lxschwalb/tone_ale/tone_ale_common/tone_ale.h

/**
 * Copyright (c) 2023 Tone Age Technology
 *
 * SPDX-License-Identifier: BSD-3-Clause
 */
void tone_ale_pins_setup();
void tone_ale_capsense_setup();
void juggle_buffers();
void tone_ale_clk_setup(float sample_rate, float system_clk);
void tone_ale_i2cv_setup(int32_t *buff, int buffsize, void interrupt_service_routine());
int32_t * mutable_data();
uint32_t i2cv_missed_deadlines(); // blocks where the ISR ran over a block period late (audio likely glitched)
void set_led(bool state);
int32_t clip_shift(int32_t x);

class Capsense
{
    int max = 0;
    int min = __INT_MAX__;
    bool pressing = false;
    bool state = false;

public:
    void reset();
    bool capsense_button(float threshold);
    bool capsense_momentary_button(int threshold);
    float capsense_return_percentage_of_max();
};

#define SIN_BUFFSIZE    256

static float sin[SIN_BUFFSIZE] = {0.00000000e+00,  2.46374492e-02,  4.92599411e-02,  7.38525275e-02,
                                    9.84002783e-02,  1.22888291e-01,  1.47301698e-01,  1.71625679e-01,
                                    1.95845467e-01,  2.19946358e-01,  2.43913720e-01,  2.67733003e-01,
                                    2.91389747e-01,  3.14869589e-01,  3.38158275e-01,  3.61241666e-01,
                                    3.84105749e-01,  4.06736643e-01,  4.29120609e-01,  4.51244057e-01,
                                    4.73093557e-01,  4.94655843e-01,  5.15917826e-01,  5.36866598e-01,
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
                                -6.45928062e-01, -6.64540179e-01, -6.82748855e-01, -7.00543038e-01,
                                -7.17911923e-01, -7.34844967e-01, -7.51331890e-01, -7.67362681e-01,
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
