lxschwalb/tone_ale/tone_ale_common/filter_coefs.h

// Coeffs for a bpf filter sweeping from fs/60 Hz to fs/6 Hz
int BPF_b0[256] = {12, 13, 13, 13, 14, 14, 15, 15, 16, 16, 16, 17, 17, 18, 18, 18, 19, 19, 20, 20, 20, 21, 21, 22, 22, 22, 23, 23, 23, 24, 24, 25, 25, 25, 26, 26, 26, 27, 27, 28, 28, 28, 29, 29, 29, 30, 30, 30, 31, 31, 31, 32, 32, 33, 33, 33, 34, 34, 34, 35, 35, 35, 36, 36, 36, 37, 37, 37, 37, 38, 38, 38, 39, 39, 39, 40, 40, 40, 41, 41, 41, 42, 42, 42, 42, 43, 43, 43, 44, 44, 44, 45, 45, 45, 45, 46, 46, 46, 47, 47, 47, 47, 48, 48, 48, 48, 49, 49, 49, 50, 50, 50, 50, 51, 51, 51, 51, 52, 52, 52, 52, 53, 53, 53, 53, 54, 54, 54, 54, 55, 55, 55, 55, 56, 56, 56, 56, 57, 57, 57, 57, 57, 58, 58, 58, 58, 59, 59, 59, 59, 60, 60, 60, 60, 60, 61, 61, 61, 61, 61, 62, 62, 62, 62, 62, 63, 63, 63, 63, 63, 64, 64, 64, 64, 64, 65, 65, 65, 65, 65, 66, 66, 66, 66, 66, 67, 67, 67, 67, 67, 67, 68, 68, 68, 68, 68, 68, 69, 69, 69, 69, 69, 69, 70, 70, 70, 70, 70, 70, 71, 71, 71, 71, 71, 71, 72, 72, 72, 72, 72, 72, 72, 73, 73, 73, 73, 73, 73, 73, 74, 74, 74, 74, 74, 74, 74, 75, 75, 75, 75, 75, 75, 75, 75, 76, 76, 76, 76, 76, 76, 76, 76, 77, 77, 77, 77};
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

// Coeffs for a hpf filter TODO
int HPF_b0[256] = {};
int HPF_b1[256] = {};
int HPF_b2[256] = {};
int HPF_a1[256] = {};
int HPF_a2[256] = {};

// Coeffs for a FIR cabsim (in reverse order)
#define CAB_BUFFSIZE    128
int cab[CAB_BUFFSIZE] = {-1, -2, -2, -3, -3, -3, -4, -4, -4, -4, -5, -5, -5, -5, -5, -6, -6, -6, -6, -6, -7, -7, -7, -7, -7, -8, -8, -8, -8, -8, -9, -9, -9, -9, -9, -10, -10, -10, -10, -10, -10, -10, -11, -11, -11, -11, -11, -11, -11, -11, -11, -11, -11, -11, -11, -11, -11, -11, -11, -11, -11, -11, -11, -11, -11, -11, -11, -11, -11, -11, -11, -11, -11, -11, -11, -11, -11, -11, -11, -11, -11, -11, -11, -11, -11, -10, -10, -10, -10, -10, -9, -10, -10, -11, -13, -15, -16, -17, -15, -10, -3, 7, 15, 18, 11, -10, -43, -83, -117, -131, -111, -52, 37, 136, 215, 245, 217, 148, 73, 22, 2, -5, -10, -12, -12, -10, -7, -3};
